741Hua/TDS-Sensor/Test/assets/images/OpAmpC_Input.jpg

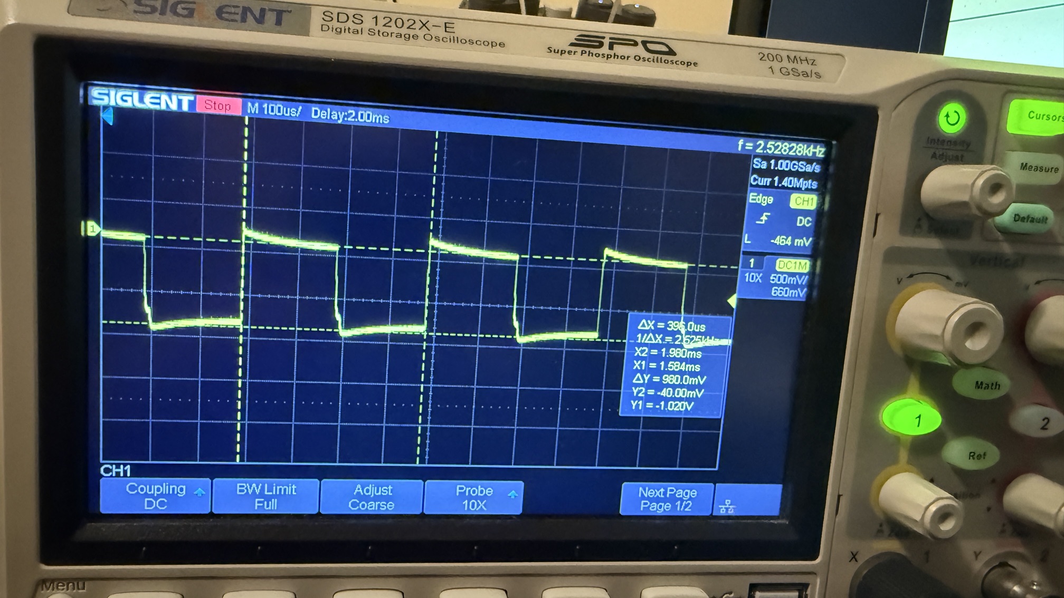
Test/assets/images/OpAmpC_Input.jpg
