741Hua/TDS-Sensor/Test/assets/images/STM32F103_Datasheet_Table_20.png

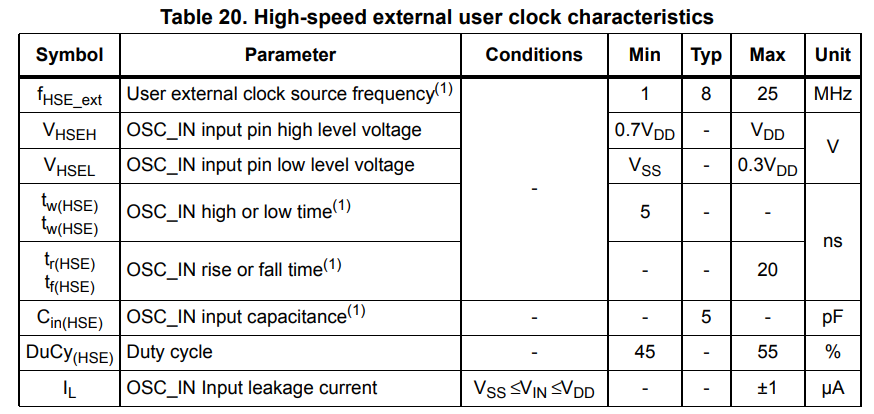
Test/assets/images/STM32F103_Datasheet_Table_20.png
