741Hua/TDS-Sensor/Test/assets/images/STM32F103_Figure_22.png

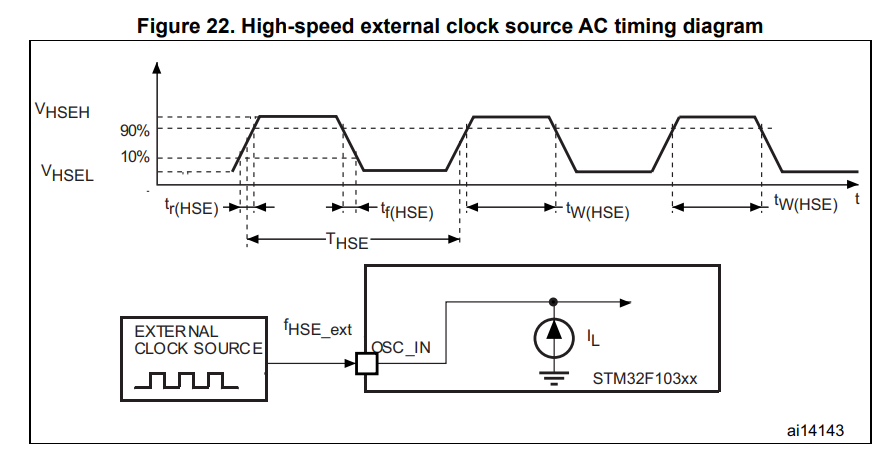
Test/assets/images/STM32F103_Figure_22.png
